mlhakimz/Robocon20/PR/Coupler kicking 10mm.SLDPRT

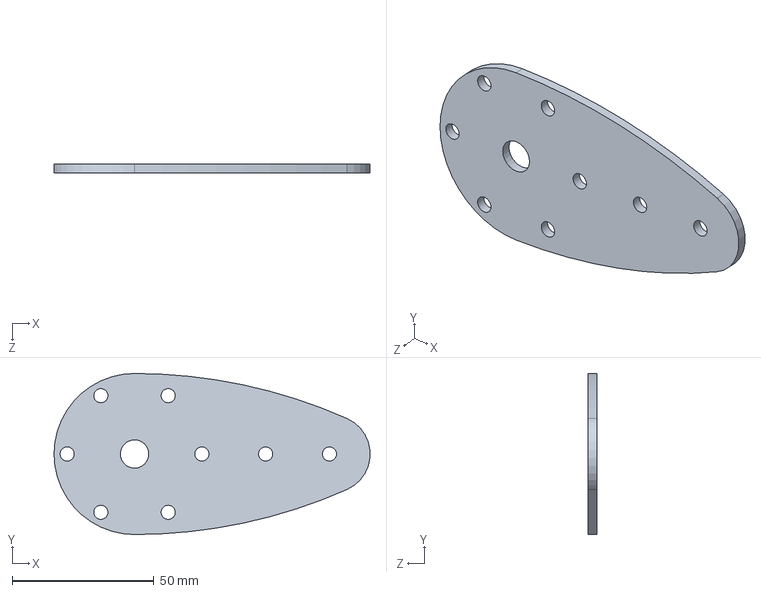
[picture p26: CAD file, 2020-11-02]
PR/Coupler kicking 10mm.SLDPRT
111.5 x 56.8 x 3.00 mm
