mlhakimz/Robocon20/PR/Pneumatic16x200 body.SLDPRT

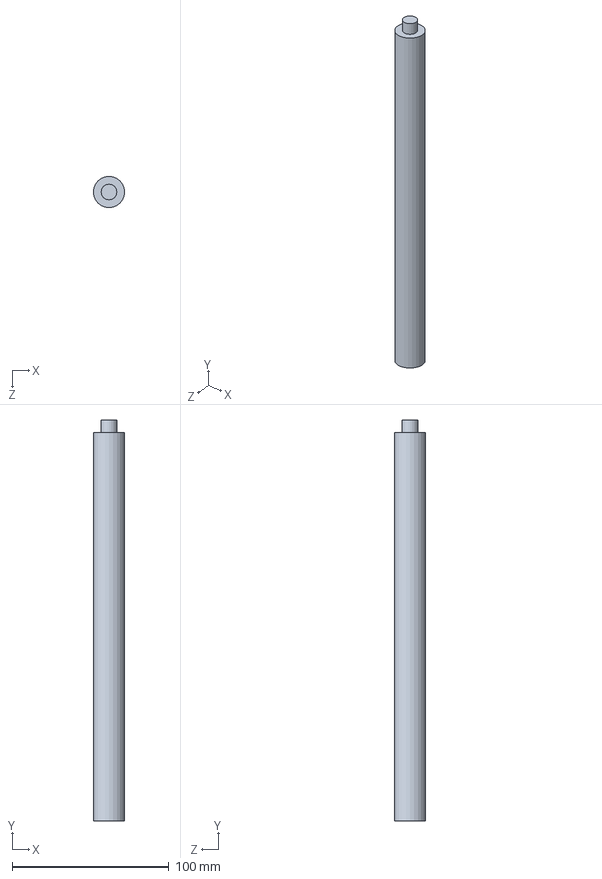
[picture p27: CAD file, 2020-11-02]
PR/Pneumatic16x200 body.SLDPRT
20.0 x 256.0 x 20.0 mm
