mlhakimz/Robocon20/TR v2/Plate_Var_Grip.SLDPRT

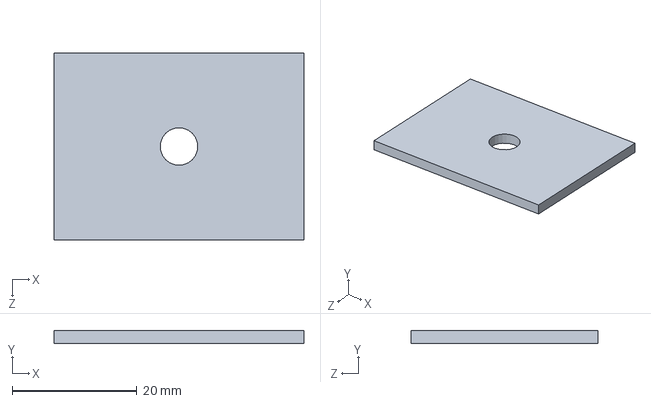
[picture p28: CAD file, 2020-11-02]
TR v2/Plate_Var_Grip.SLDPRT
40.0 x 2.00 x 30.0 mm
