mlhakimz/Robocon20/PR/Throwing Arm.SLDPRT

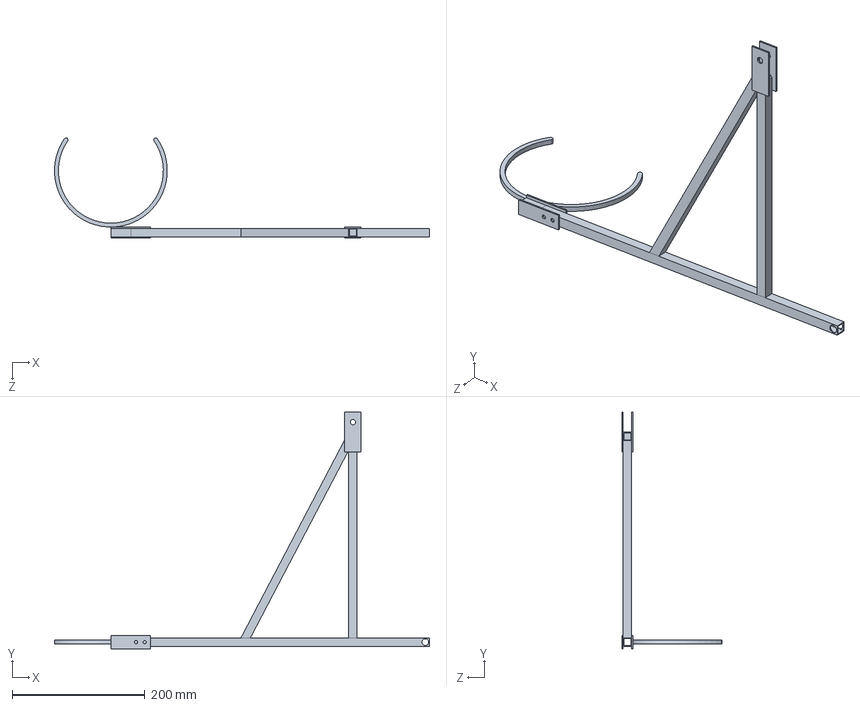
[picture p29: CAD file, 2020-11-02]
PR/Throwing Arm.SLDPRT
564.9 x 356.4 x 151.2 mm
