mlhakimz/Robocon20/TR v2/Pneumatic_Body_125.SLDPRT

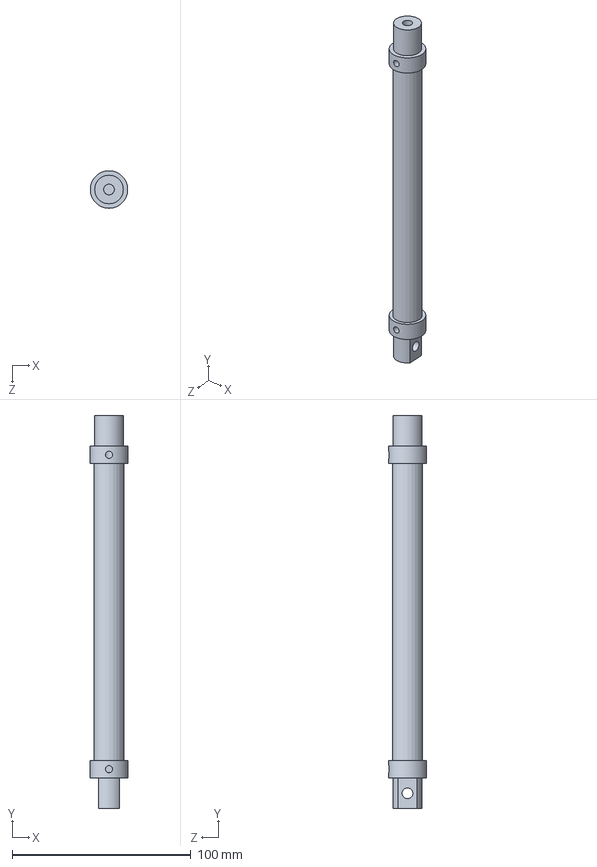
[picture p30: CAD file, 2020-11-02]
TR v2/Pneumatic_Body_125.SLDPRT
21.0 x 220.0 x 21.0 mm
