mlhakimz/Robocon20/TR v2/TR BASE.SLDPRT

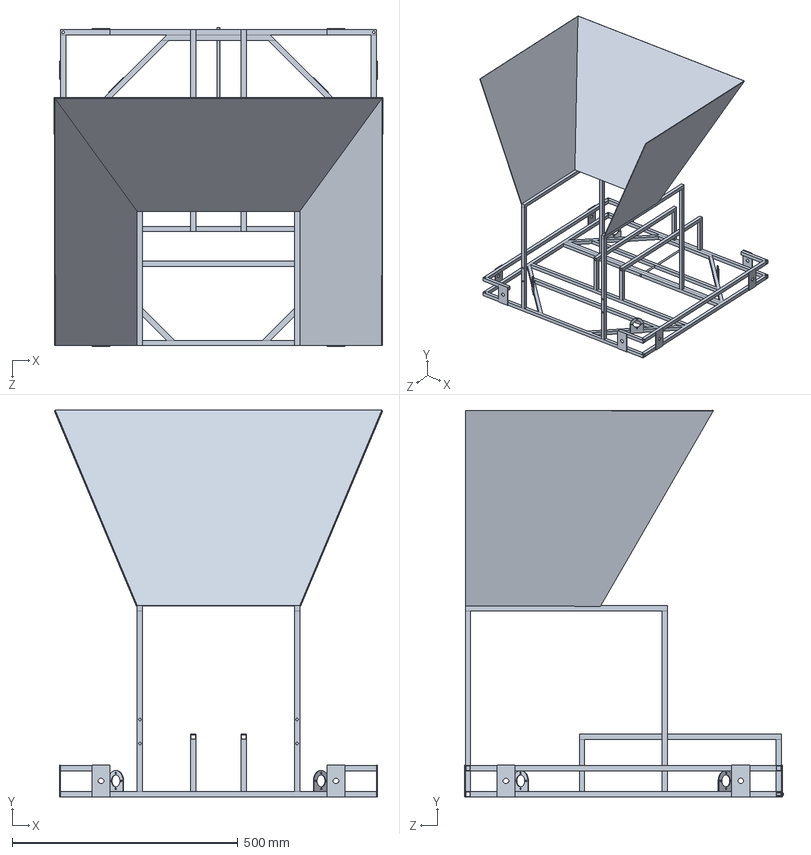
[picture p31: CAD file, 2020-11-02]
TR v2/TR BASE.SLDPRT
727.7 x 857.0 x 707.0 mm
