mlhakimz/Robocon20/TR v2/Rod_300.SLDPRT

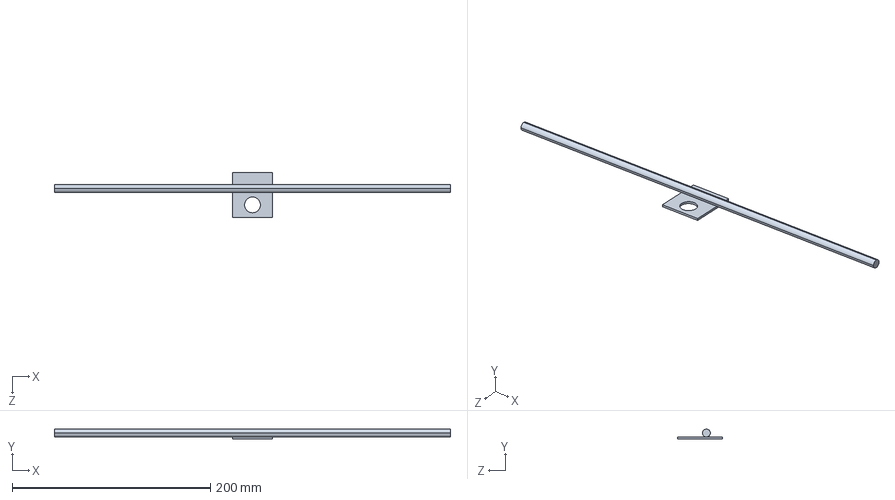
[picture p32: CAD file, 2020-11-02]
TR v2/Rod_300.SLDPRT
400.0 x 10.0 x 45.0 mm
