mlhakimz/Robocon20/PR/Linear Bearing 8mm ID.step

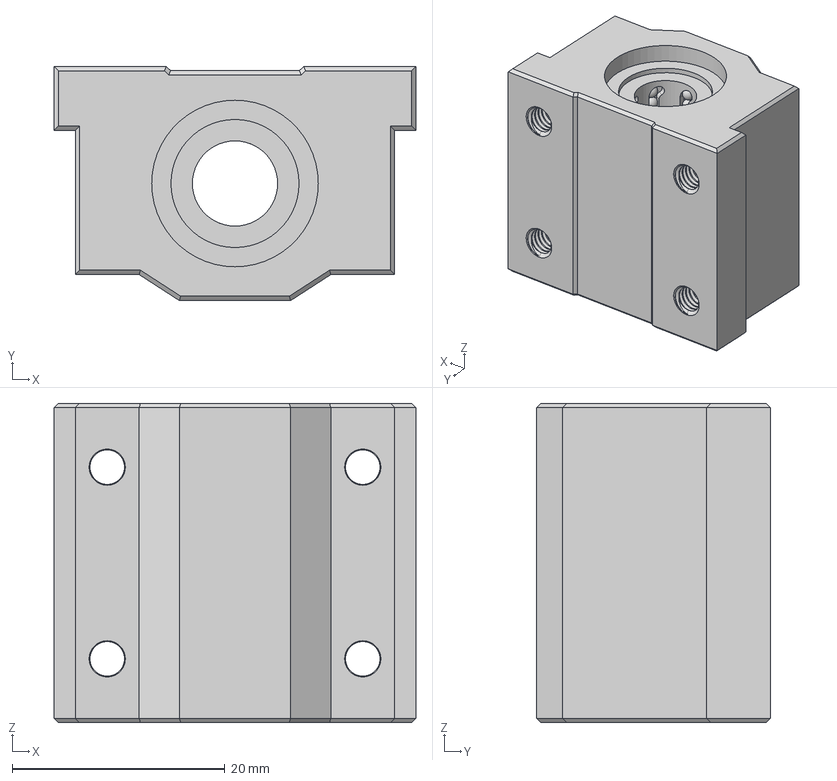
[picture p33: CAD file, 2020-11-02]
PR/Linear Bearing 8mm ID.step
34.0 x 22.0 x 30.0 mm
