mlhakimz/Robocon20/PR/Bearing Plate.SLDPRT

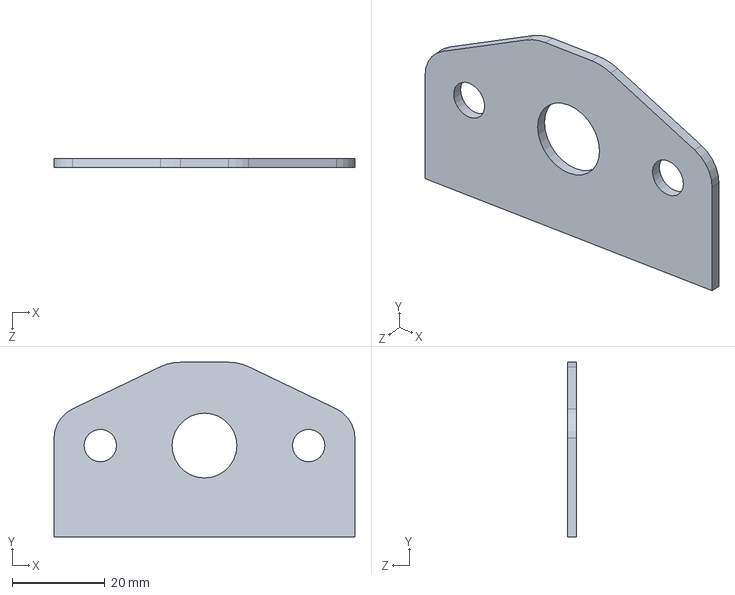
[picture p34: CAD file, 2020-11-02]
PR/Bearing Plate.SLDPRT
65.0 x 37.7 x 2.00 mm
