mlhakimz/Robocon20/TR v2/Platform_Receive.SLDPRT

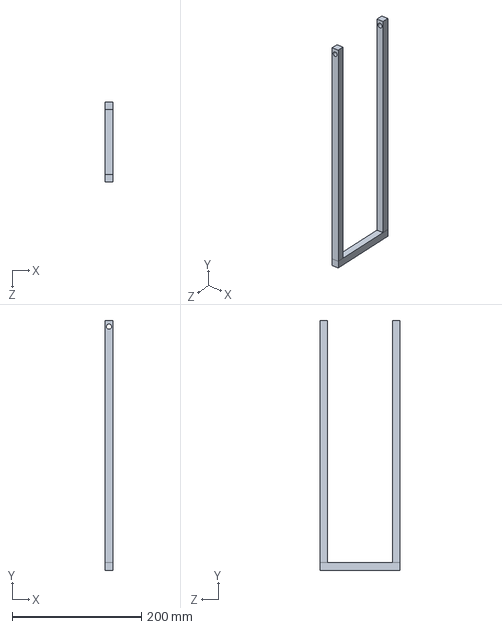
[picture p35: CAD file, 2020-11-02]
TR v2/Platform_Receive.SLDPRT
12.0 x 387.0 x 124.0 mm
