mlhakimz/Robocon20/PR/Kicking Leg.SLDPRT

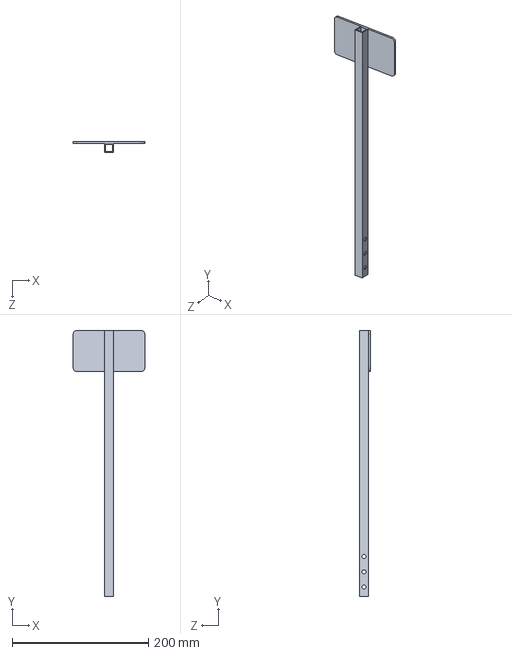
[picture p36: CAD file, 2020-11-02]
PR/Kicking Leg.SLDPRT
105.0 x 390.0 x 15.7 mm
