mlhakimz/Robocon20/PR/Pneumatic16x200 piston.SLDPRT

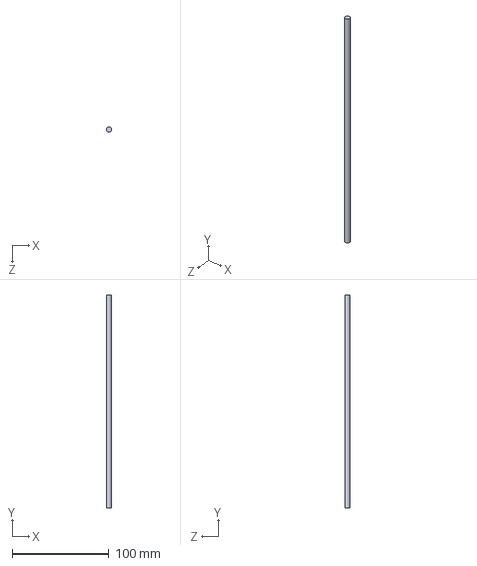
[picture p37: CAD file, 2020-11-02]
PR/Pneumatic16x200 piston.SLDPRT
5.50 x 220.0 x 5.50 mm
