mlhakimz/Robocon20/PR/Shaft 10mm diameter 300mm length.SLDPRT

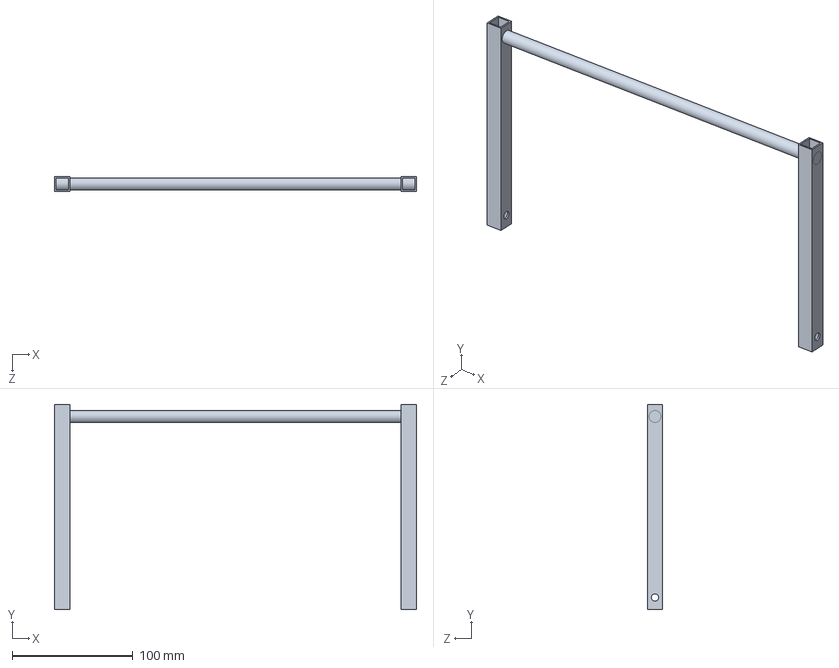
[picture p38: CAD file, 2020-11-02]
PR/Shaft 10mm diameter 300mm length.SLDPRT
300.0 x 170.0 x 12.7 mm
