mlhakimz/Robocon20/PR/Passing Mechanism Base.SLDPRT

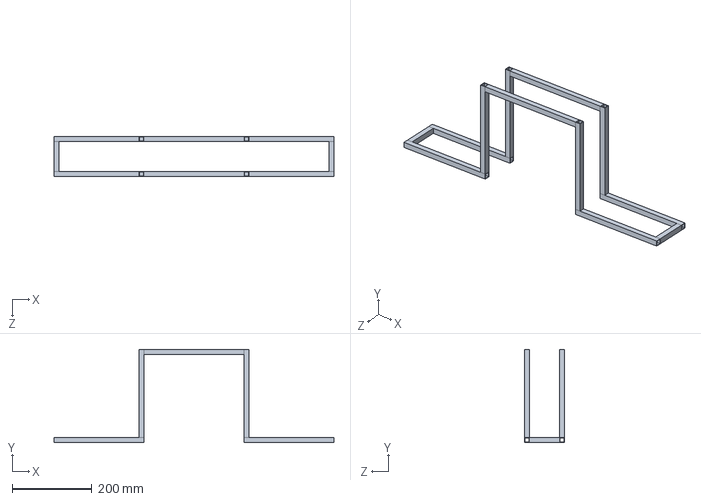
[picture p39: CAD file, 2020-11-02]
PR/Passing Mechanism Base.SLDPRT
700.0 x 232.7 x 100.4 mm
