mlhakimz/Robocon20/PR/Pneumatic Bottom Slot.SLDPRT

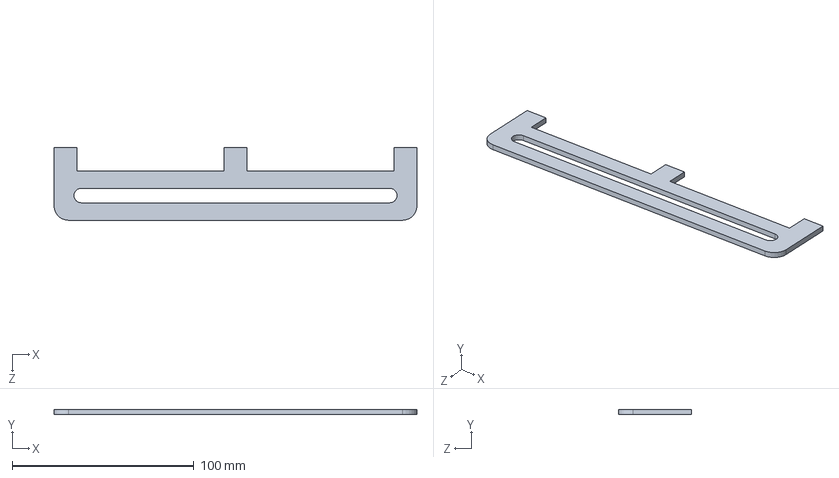
[picture p40: CAD file, 2020-11-02]
PR/Pneumatic Bottom Slot.SLDPRT
200.0 x 3.00 x 40.0 mm
