mlhakimz/Robocon20/PR/Base PR.SLDPRT

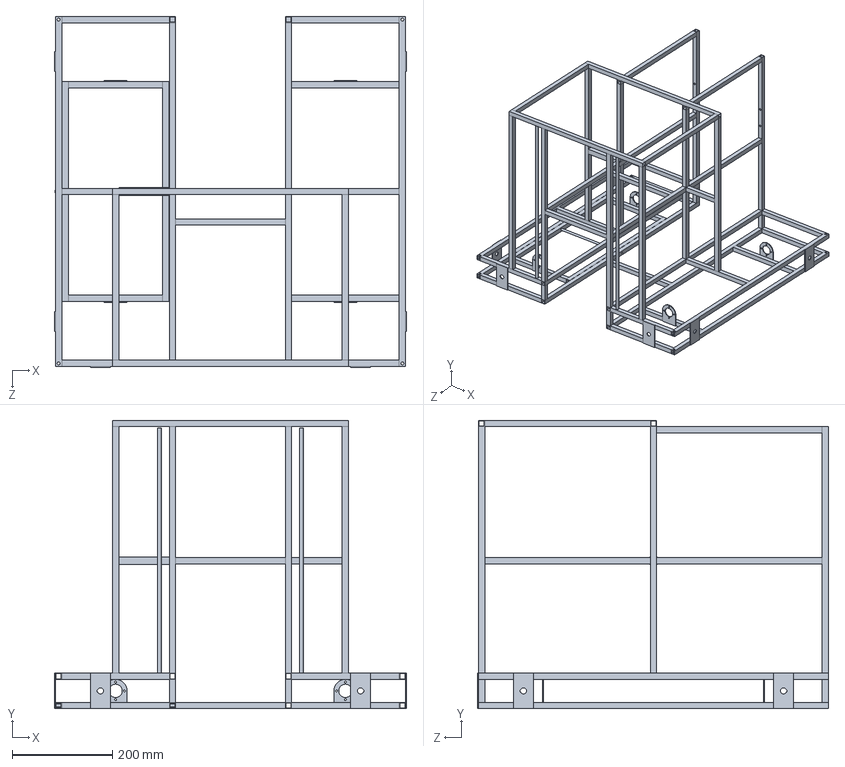
[picture p41: CAD file, 2020-11-02]
PR/Base PR.SLDPRT
704.0 x 576.8 x 702.0 mm
