mlhakimz/Robocon20/ROBOCON2020_v3/KickBall.ino

//void KickBall() {
//  kickflag = 5;
//  if (kickflag != 0) {
//    digitalWrite(DIRKIK, LOW);
//    analogWrite(PWMKIK, 150);
//  }
//  if (kickflag == 0) {
//    analogWrite(PWMKIK, 0);
//  }
//  if (ir1 == 1) {
//    kickflag--;
//    if (kickflag < 0) {
//      kickflag = 0;
//    }
//  }
//}
